sabanekko3/sabanekko_PCB_meishi/2024_namecard.kicad_sch

## KiCad design 2024_namecard.kicad_sch (2024-01-16)

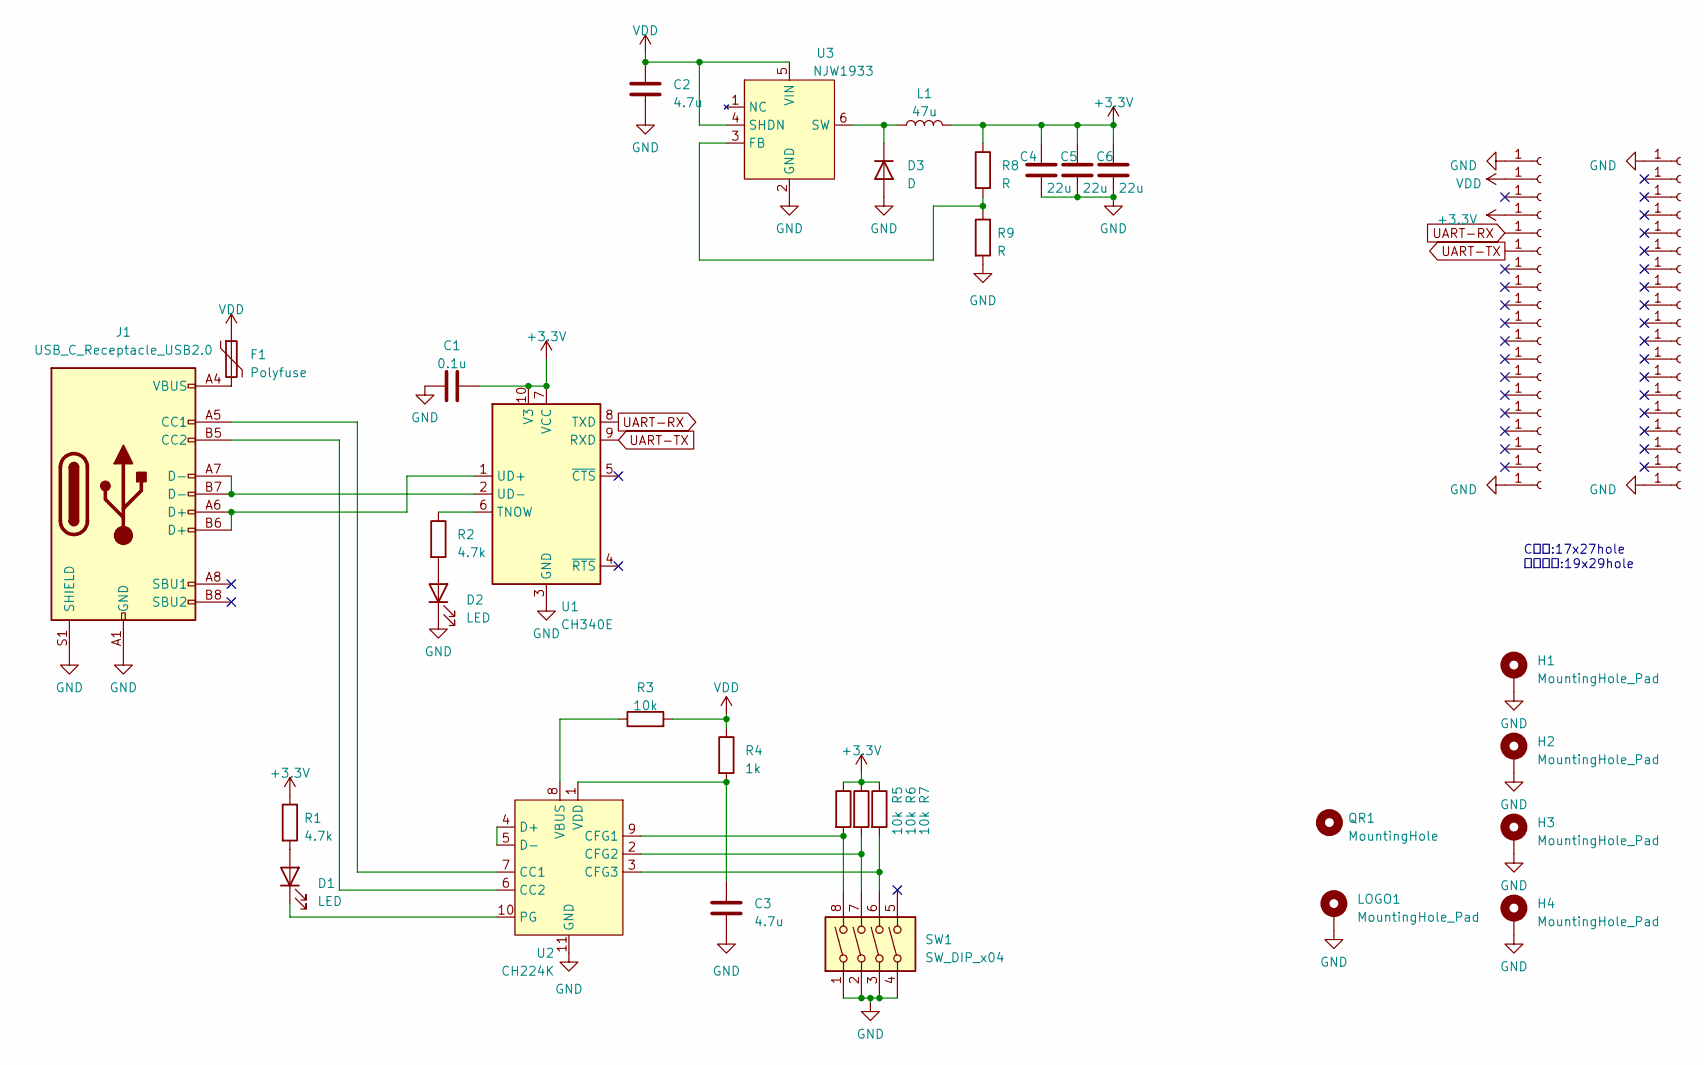
[picture p12: schematic 2024_namecard.kicad_sch]

Parts:
C1: 0.1u; C_0603_1608Metric_Pad1.08x0.95mm_HandSolder
C2, C3: 4.7u; C_0805_2012Metric_Pad1.18x1.45mm_HandSolder
C4, C5, C6: 22u; C_1206_3216Metric_Pad1.33x1.80mm_HandSolder
D1, D2: LED; LED_0603_1608Metric_Pad1.05x0.95mm_HandSolder
D3: D; D_SOD-123
F1: Polyfuse; Fuse_0805_2012Metric_Pad1.15x1.40mm_HandSolder
H1, H2, H3, H4: MountingHole_Pad; MountingHole_3.2mm_M3_ISO14580_Pad
J1: USB_C_Receptacle_USB2.0; USB_C_Receptacle_GCT_USB4105-xx-A_16P_TopMnt_Horizontal; LCSC C165948
J2, J3, J4, J5, J6, J7, J8, J9, J10, J11, J12, J13, J14, J15, J16, J17, J18, J19, J20, J21, J22, J23, J24, J25, J26, J27, J28, J29, J30, J31, J32, J33, J34, J35, J36, J37, J38, J39: Conn_01x01_Socket; through_hole_universal
L1: 47u; L_Taiyo-Yuden_NR-10050_9.8x10.0mm_HandSoldering
LOGO1: MountingHole_Pad; sabanegi
QR1: MountingHole; sabanekko_PCB_meishi_QR11x11
R1, R2: 4.7k; R_0603_1608Metric_Pad0.98x0.95mm_HandSolder
R3, R5, R6, R7: 10k; R_0603_1608Metric_Pad0.98x0.95mm_HandSolder
R4: 1k; R_0603_1608Metric_Pad0.98x0.95mm_HandSolder
R8, R9: R; R_0603_1608Metric_Pad0.98x0.95mm_HandSolder
SW1: SW_DIP_x04; SW_DIP_SPSTx04_Slide_Copal_CHS-04B_W7.62mm_P1.27mm
U1: CH340E; MSOP-10_3x3mm_P0.5mm
U2: CH224K; ESSOP-10_3.9x4.9mm_P1.00mm; LCSC C970725
U3: NJW1933; SOT-23-6_Handsoldering

Connections:
+3.3V: C1.2, C4.1, C5.1, C6.1, J5.1, L1.2, R1.1, R5.1, R6.1, R7.1, R8.1, U1.7 (VCC), U1.10 (V3)
GND: C1.1, C2.2, C3.2, C4.2, C5.2, C6.2, D2.1 (K), D3.2 (A), H1.1, H2.1, H3.1, H4.1, J1.A1 (GND), J1.A12 (GND), J1.B1 (GND), J1.B12 (GND), J1.S1 (SHIELD), J2.1, J20.1, J21.1, J39.1, LOGO1.1, R9.2, SW1.1, SW1.2, SW1.3, SW1.4, U1.3 (GND), U2.11 (GND), U3.2 (GND)
unnamed: C3.1, R4.2, U2.1 (VDD)
unnamed: D1.1 (K), U2.10 (PG)
unnamed: D1.2 (A), R1.2
unnamed: D2.2 (A), R2.2
unnamed: D3.1 (K), L1.1, U3.6 (SW)
unnamed: F1.2, J1.A4 (VBUS), J1.A9 (VBUS), J1.B4 (VBUS), J1.B9 (VBUS)
unnamed: J1.A5 (CC1), U2.7 (CC1)
unnamed: J1.A6 (D+), J1.B6 (D+), U1.1 (UD+)
unnamed: J1.A7 (D-), J1.B7 (D-), U1.2 (UD-)
unnamed: J1.B5 (CC2), U2.6 (CC2)
unnamed: R2.1, U1.6 (TNOW)
unnamed: R3.1, U2.8 (VBUS)
unnamed: R5.2, SW1.8, U2.9 (CFG1)
unnamed: R6.2, SW1.7, U2.2 (CFG2)
unnamed: R7.2, SW1.6, U2.3 (CFG3)
unnamed: R8.2, R9.1, U3.3 (FB)
unnamed: U2.4 (D+), U2.5 (D-)
UART-RX: J6.1, U1.8 (TXD)
UART-TX: J7.1, U1.9 (RXD)
VDD: C2.1, F1.1, J3.1, R3.2, R4.1, U3.4 (SHDN), U3.5 (VIN)

Notes on the sheet:
C基板:17x27hole この基板:19x29hole
